zhdo1983/IMP-PLAYER/ESP32-MAX98357-I2S-V001/src/icons.h

#ifndef ICONS_H
#define ICONS_H

#include <Arduino.h>

const uint8_t speaker_icon[] U8X8_PROGMEM = {
    0x00, 0x00, 0x80, 0x01, 0xC0, 0x03, 0xE0, 0x07, 0xF0, 0x0F, 0xF0, 0x0F,
    0xF0, 0x0F, 0xF0, 0x0F, 0xF0, 0x0F, 0xF0, 0x0F, 0xE0, 0x07, 0xC0, 0x03,
    0x80, 0x01, 0x00, 0x00, 0x00, 0x00, 0x00, 0x00
};

const uint8_t cloud_icon_32x32[] U8X8_PROGMEM = {
    0x00, 0x00, 0x00, 0x00, 0x00, 0x00, 0x00, 0x00,
    0x00, 0x00, 0x00, 0x00, 0x00, 0x00, 0x00, 0x00,
    0x00, 0x00, 0x00, 0x00, 0x00, 0x00, 0x00, 0x00,
    0x00, 0x00, 0x00, 0x00, 0x00, 0x00, 0x00, 0x00,
    0x00, 0x00, 0x00, 0x00, 0x00, 0x00, 0x00, 0xE0,
    0x07, 0x00, 0x00, 0x00, 0x00, 0x00, 0x00, 0x00,
    0x00, 0x00, 0x00, 0xFC, 0x1F, 0x00, 0x00, 0x00,
    0x00, 0x00, 0x00, 0x00, 0x00, 0xFF, 0xFF, 0x03,
    0x00, 0x00, 0x00, 0x00, 0x80, 0xFF, 0xFF, 0x07,
    0x00, 0x00, 0x00, 0x00, 0xF8, 0xFF, 0xFF, 0x0F,
    0x00, 0x00, 0x00, 0x00, 0xFC, 0xFF, 0xFF, 0x1F,
    0x00, 0x00, 0x00, 0x00, 0xFE, 0xFF, 0xFF, 0x3F,
    0x00, 0x00, 0x00, 0x00, 0xFF, 0xFF, 0xFF, 0x7F,
    0x00, 0x00, 0x00, 0x80, 0xFF, 0xFF, 0xFF, 0x7F,
    0x00, 0x00, 0x00, 0xC0, 0xFF, 0xFF, 0xFF, 0xFF,
    0x00, 0x00, 0x00, 0xF0, 0xFF, 0xFF, 0xFF, 0xFF,
    0x00, 0x00, 0x00, 0xF8, 0xFF, 0xFF, 0xFF, 0xFF,
    0x00, 0x00, 0x00, 0xFC, 0xFF, 0xFF, 0xFF, 0xFF,
    0x00, 0x00, 0x00, 0xFE, 0xFF, 0xFF, 0xFF, 0xFF,
    0x00, 0x00, 0x00, 0xFF, 0x00, 0xFE, 0xFF, 0x7F,
    0x00, 0x00, 0x80, 0x7F, 0x00, 0xFC, 0xFF, 0x3F,
    0x00, 0x00, 0xC0, 0x3F, 0x00, 0xF8, 0xFF, 0x1F,
    0x00, 0x00, 0xE0, 0x1F, 0x00, 0xF0, 0xFF, 0x0F,
    0x00, 0x00, 0xF0, 0x0F, 0x00, 0xE0, 0xFF, 0x07,
    0x00, 0x00, 0xF8, 0x07, 0x00, 0xC0, 0xFF, 0x03,
    0x00, 0x00, 0xFC, 0x03, 0x00, 0x80, 0x7F, 0x00,
    0x00, 0x00, 0xFF, 0x01, 0x00, 0x00, 0x00, 0x00,
    0x00, 0x80, 0xFF, 0x00, 0x00, 0x00, 0x00, 0x00,
    0x00, 0xC0, 0x7F, 0x00, 0x00, 0x00, 0x00, 0x00,
    0x00, 0xE0, 0x3F, 0x00, 0x00, 0x00, 0x00, 0x00,
    0x00, 0xF0, 0x1F, 0x00, 0x00, 0x00, 0x00, 0x00,
    0x00, 0xF8, 0x0F, 0x00, 0x00, 0x00, 0x00, 0x00,
    0x00, 0xFC, 0x07, 0x00, 0x00, 0x00, 0x00, 0x00,
    0x00, 0xFF, 0x03, 0x00, 0x00, 0x00, 0x00, 0x00
};

// 暂停图标（16×16 px，XBM格式，LSB-first，PROGMEM存储）
// 两条竖矩形柱，居中显示，适合128×64 OLED
// 使用方式：u8g2.drawXBMP(x, y, 16, 16, pause_icon)
const uint8_t pause_icon[] U8X8_PROGMEM = {
    // 每行2字节，共16行；左柱：bit3-5，右柱：bit10-12（LSB排列）
    0x38, 0x1C,   // row 0
    0x38, 0x1C,   // row 1
    0x38, 0x1C,   // row 2
    0x38, 0x1C,   // row 3
    0x38, 0x1C,   // row 4
    0x38, 0x1C,   // row 5
    0x38, 0x1C,   // row 6
    0x38, 0x1C,   // row 7
    0x38, 0x1C,   // row 8
    0x38, 0x1C,   // row 9
    0x38, 0x1C,   // row 10
    0x38, 0x1C,   // row 11
    0x38, 0x1C,   // row 12
    0x38, 0x1C,   // row 13
    0x38, 0x1C,   // row 14
    0x38, 0x1C    // row 15
};

// 播放图标（16×16 px，XBM格式，LSB-first，PROGMEM存储）
// 向右的三角形，适合128×64 OLED
// 使用方式：u8g2.drawXBMP(x, y, 16, 16, play_icon)
const uint8_t play_icon[] U8X8_PROGMEM = {
    0x02, 0x00,   // row 0   : .X..............
    0x06, 0x00,   // row 1   : .XX.............
    0x0E, 0x00,   // row 2   : .XXX............
    0x1E, 0x00,   // row 3   : .XXXX...........
    0x3E, 0x00,   // row 4   : .XXXXX..........
    0x7E, 0x00,   // row 5   : .XXXXXX.........
    0xFE, 0x00,   // row 6   : .XXXXXXX........
    0xFE, 0x01,   // row 7   : .XXXXXXXX.......
    0xFE, 0x01,   // row 8   : .XXXXXXXX.......
    0xFE, 0x00,   // row 9   : .XXXXXXX........
    0x7E, 0x00,   // row 10  : .XXXXXX.........
    0x3E, 0x00,   // row 11  : .XXXXX..........
    0x1E, 0x00,   // row 12  : .XXXX...........
    0x0E, 0x00,   // row 13  : .XXX............
    0x06, 0x00,   // row 14  : .XX.............
    0x02, 0x00    // row 15  : .X..............
};

// WiFi信号强度图标 —— 低（16×8 px，XBM格式）
// 仅底部1格亮，其余空心弧
// 使用方式：u8g2.drawXBMP(x, y, 16, 8, signalLow)
const uint8_t signalLow[] U8X8_PROGMEM = {
    0x00, 0x00,   // row 0  (顶弧，低信号时不显示)
    0x00, 0x00,   // row 1
    0x00, 0x00,   // row 2  (中弧，低信号时不显示)
    0x00, 0x00,   // row 3
    0xE0, 0x03,   // row 4  : ........XXXXX...  (中弧轮廓，灰显)  → 实际不显示，只显示底格
    0x00, 0x00,   // row 5
    0xC0, 0x01,   // row 6  : .........XXX....  (底格实心)
    0xC0, 0x01    // row 7  : .........XXX....
};

// WiFi信号强度图标 —— 中（16×8 px，XBM格式）
// 底部2格亮
const uint8_t signalMedium[] U8X8_PROGMEM = {
    0x00, 0x00,   // row 0  (顶弧，中信号时不显示)
    0x00, 0x00,   // row 1
    0xF8, 0x0F,   // row 2  : .....XXXXXXXX...  (中弧)
    0x00, 0x00,   // row 3
    0xE0, 0x03,   // row 4  : .......XXXXX....  (内弧实心)
    0x00, 0x00,   // row 5
    0xC0, 0x01,   // row 6  : .........XXX....  (底格实心)
    0xC0, 0x01    // row 7
};

// WiFi信号强度图标 —— 强（16×8 px，XBM格式）
// 全部3格亮
const uint8_t signalHigh[] U8X8_PROGMEM = {
    0xFE, 0x3F,   // row 0  : .XXXXXXXXXXXXXXXXX..  (顶外弧)
    0x00, 0x00,   // row 1
    0xF8, 0x0F,   // row 2  : .....XXXXXXXX....  (中弧)
    0x00, 0x00,   // row 3
    0xE0, 0x03,   // row 4  : .......XXXXX....  (内弧)
    0x00, 0x00,   // row 5
    0xC0, 0x01,   // row 6  : .........XXX....  (底格实心)
    0xC0, 0x01    // row 7
};


// =====================================================
// 选择界面大图标（XBM格式，LSB-first，PROGMEM存储）
// 尺寸：52×44 px，每行7字节，共44行 = 308字节/图标
// 使用：u8g2.drawXBMP(x, y, 52, 44, ICON_WIFI_BIG)
// =====================================================

// 网络播放器：耳机轮廓 + 音频波形柱（52×44）
static const unsigned char ICON_WIFI_BIG[308] PROGMEM = {
  0x00, 0x00, 0x00, 0x00, 0x00, 0x00, 0x00, 0x00,
  0x00, 0x00, 0x00, 0x00, 0x00, 0x00, 0x00, 0x00,
  0x00, 0x00, 0x00, 0x00, 0x00, 0x00, 0x00, 0x00,
  0x00, 0x00, 0x00, 0x00, 0x00, 0x00, 0x00, 0x00,
  0x00, 0x00, 0x00, 0x00, 0x00, 0x00, 0x00, 0x00,
  0x00, 0x00, 0x00, 0x00, 0xC0, 0x7F, 0x00, 0x00,
  0x00, 0x00, 0x00, 0xF8, 0xFF, 0x03, 0x00, 0x00,
  0x00, 0x00, 0xFE, 0xFF, 0x0F, 0x00, 0x00, 0x00,
  0x80, 0x3F, 0x80, 0x3F, 0x00, 0x00, 0x00, 0xC0,
  0x07, 0x00, 0x7C, 0x00, 0x00, 0x00, 0xE0, 0x01,
  0x00, 0xF0, 0x00, 0x00, 0x00, 0x70, 0x00, 0x00,
  0xC0, 0x01, 0x00, 0x00, 0x38, 0x00, 0x00, 0x80,
  0x03, 0x00, 0x00, 0x1C, 0x00, 0x00, 0x00, 0x07,
  0x00, 0x00, 0x0E, 0x00, 0x00, 0x00, 0x0E, 0x00,
  0x00, 0x06, 0x00, 0x00, 0x00, 0x0C, 0x00, 0x00,
  0x03, 0x00, 0x00, 0x00, 0x18, 0x00, 0x00, 0x01,
  0xC0, 0x01, 0x00, 0x10, 0x00, 0x00, 0x01, 0xC0,
  0x01, 0x00, 0x10, 0x00, 0x80, 0x00, 0xC0, 0x01,
  0x00, 0x20, 0x00, 0x80, 0x00, 0xC0, 0x01, 0x00,
  0x20, 0x00, 0xFC, 0x01, 0xC0, 0x39, 0x00, 0xF0,
  0x07, 0xFC, 0x01, 0xC0, 0x39, 0x00, 0xF0, 0x05,
  0xFC, 0x01, 0xC0, 0x39, 0x00, 0xF0, 0x05, 0xFC,
  0x01, 0xCE, 0x39, 0x00, 0xF0, 0x05, 0xFC, 0x01,
  0xCE, 0x39, 0x00, 0xF0, 0x05, 0xFC, 0x01, 0xCE,
  0x39, 0x00, 0xF0, 0x05, 0xFC, 0x01, 0xCE, 0x39,
  0x07, 0xF0, 0x05, 0xFC, 0x01, 0xCE, 0x39, 0x07,
  0xF0, 0x05, 0xFC, 0x01, 0xCE, 0x39, 0x07, 0xF0,
  0x05, 0xFC, 0x71, 0xCE, 0x39, 0x07, 0xF0, 0x05,
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
  0x08, 0x00, 0x00, 0x01, 0x00, 0x0E, 0x00, 0x08,
  0x00, 0x00, 0x01, 0x00, 0x1F, 0x00, 0x08, 0x00,
  0x00, 0x01, 0x00, 0x1F, 0x00, 0x08, 0x00, 0x00,
  0x01, 0x00, 0x1F, 0x00, 0x08, 0x00, 0x00, 0x02,
  0x00, 0x0E, 0x00, 0x04, 0x00, 0x00, 0xFC, 0xFF,
  0xFF, 0xFF, 0x03, 0x00
};

#endif
